techmech-keeb/OLSK60_v2/docs/images/cherry-mx-switch-views.png

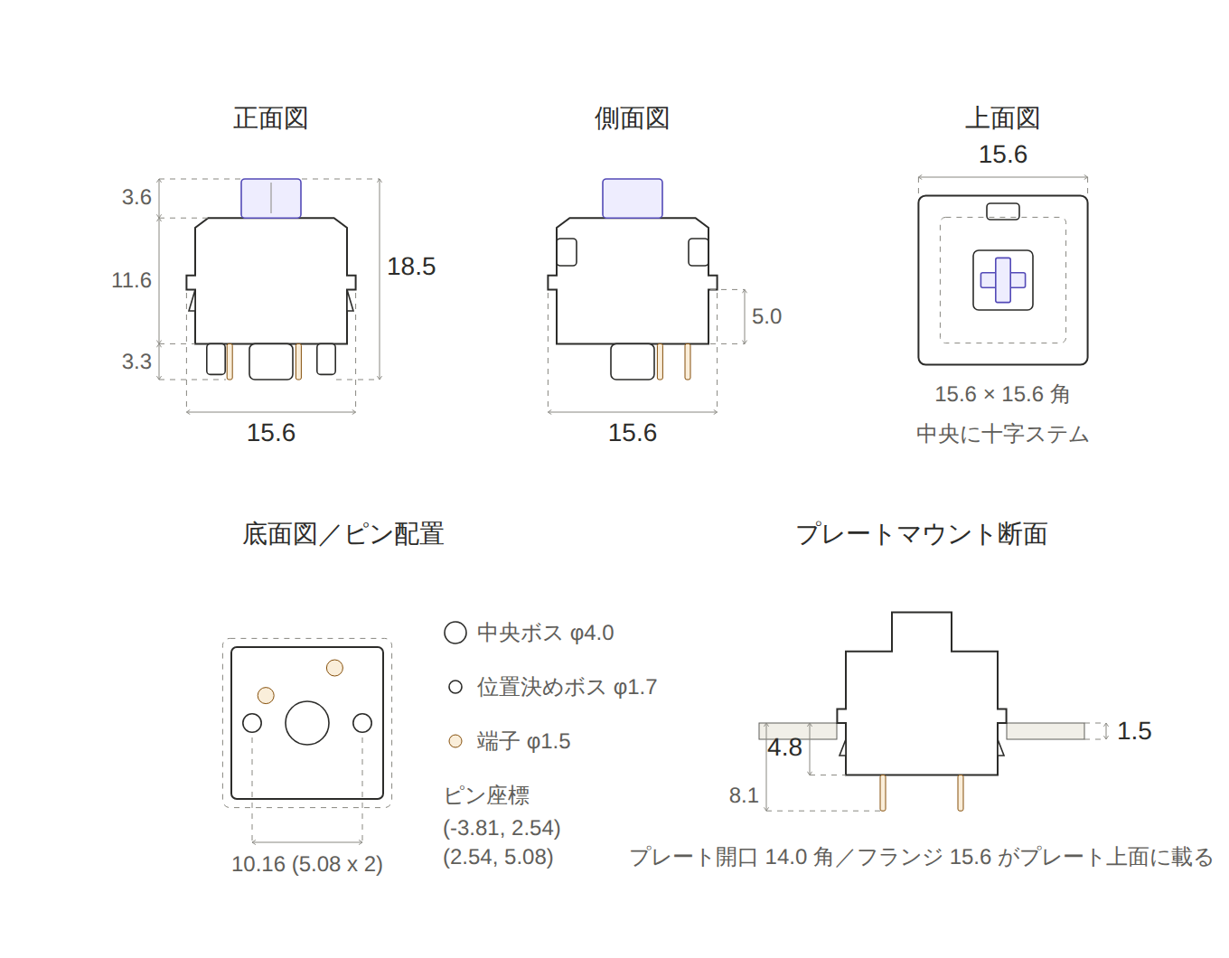
docs/images/cherry-mx-switch-views.png
