techmech-keeb/OLSK60_v2/docs/images/keycap-sizes-3split.png

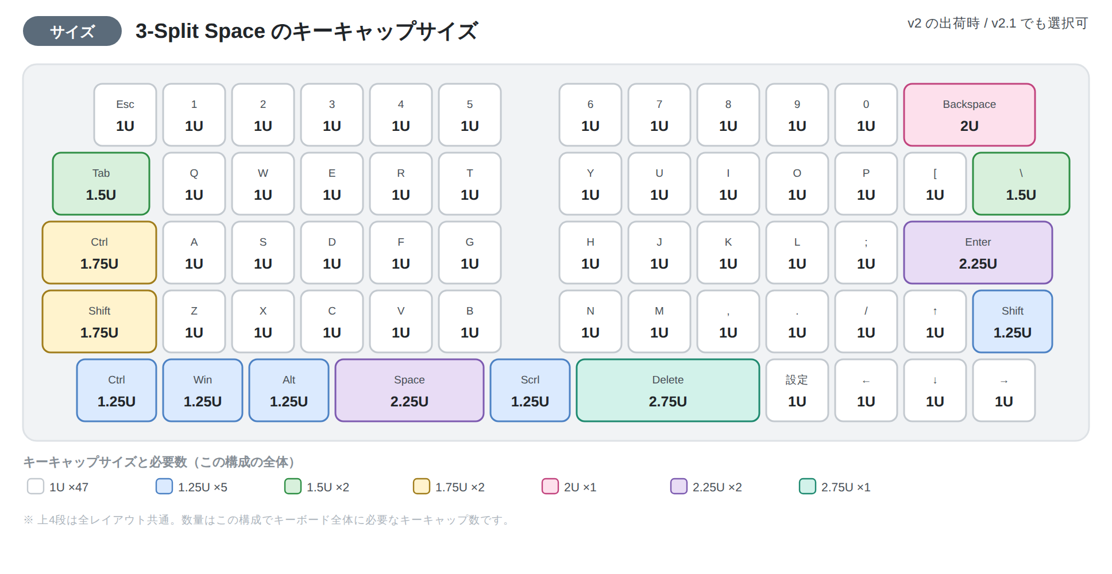
docs/images/keycap-sizes-3split.png
