techmech-keeb/OLSK60_v2/docs/images/keycap-sizes-5split.png

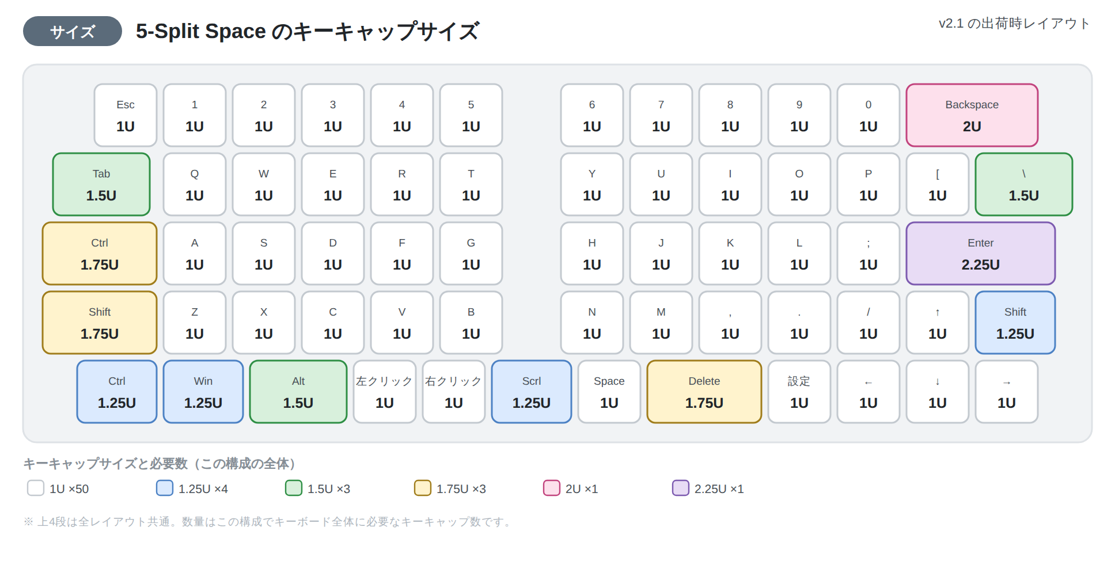
docs/images/keycap-sizes-5split.png
