techmech-keeb/OLSK60_v2/docs/images/layer2-settings.png

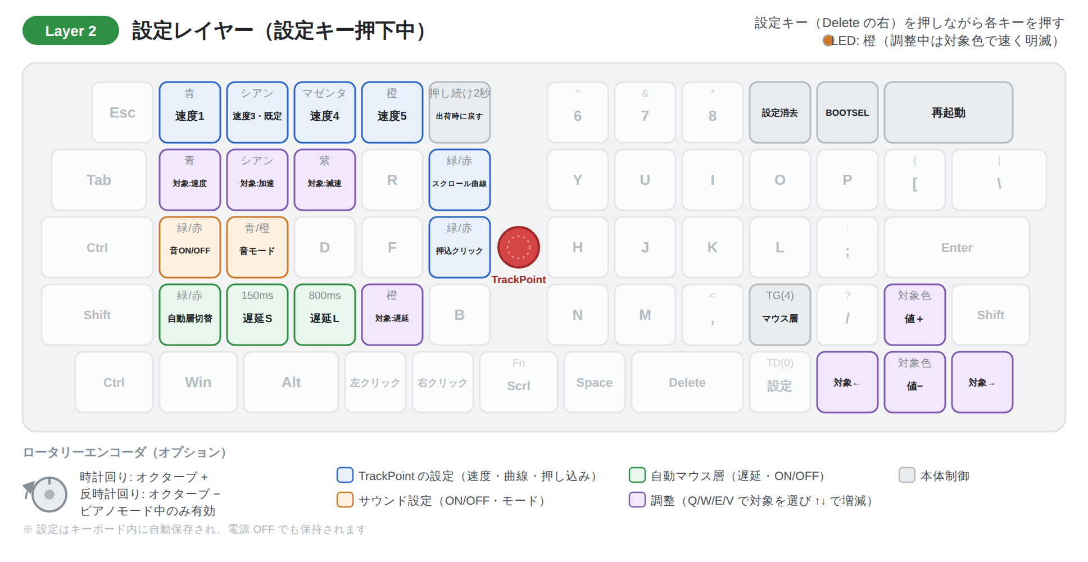
docs/images/layer2-settings.png
