techmech-keeb/OLSK60_v2/docs/images/layer3-mouse.png

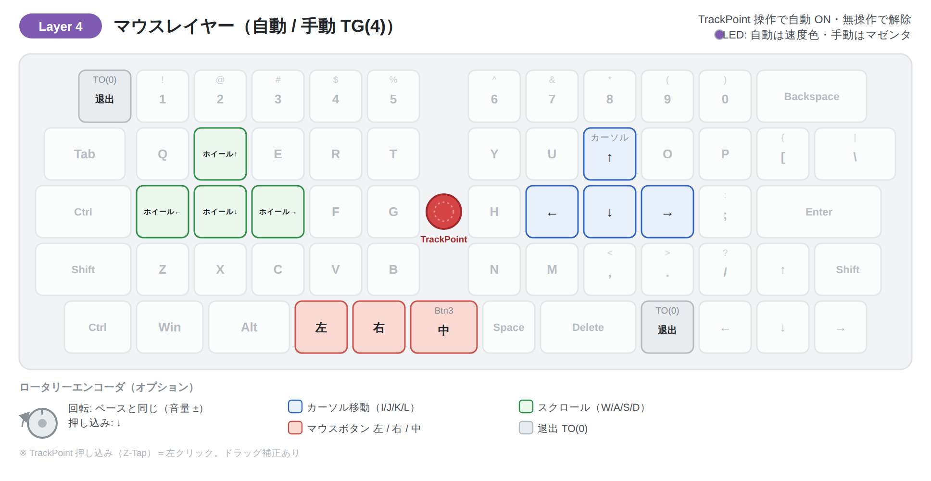
docs/images/layer3-mouse.png
