techmech-keeb/OLSK60_v2/docs/images/stab-positions.png

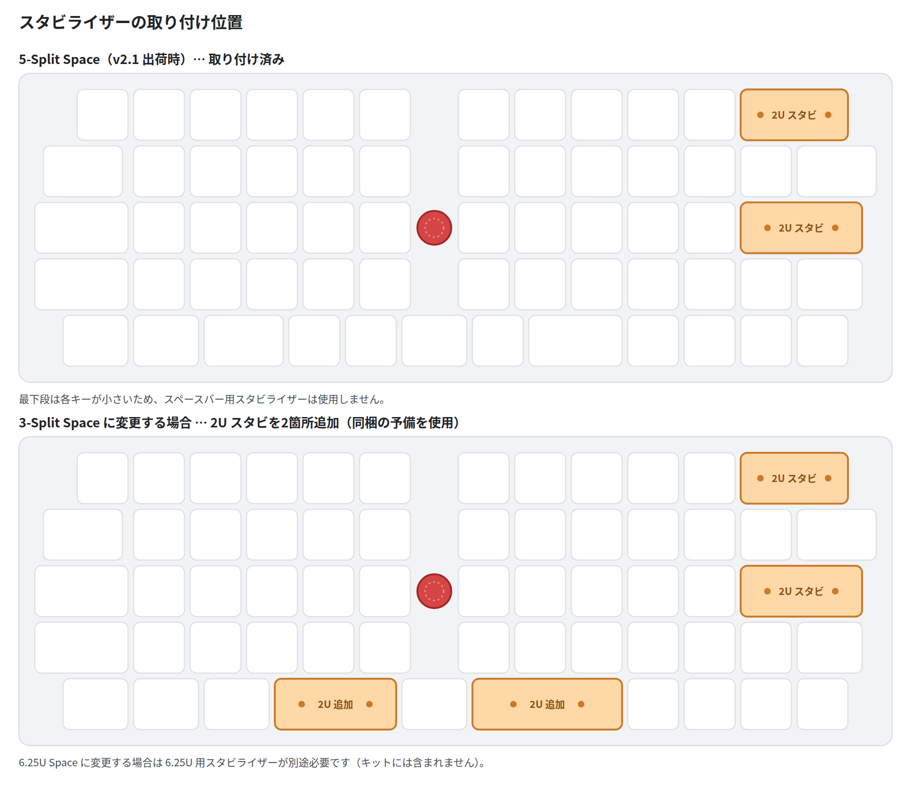
docs/images/stab-positions.png
