techmech-keeb/OLSK60_v2/docs/images/switch-mount.png

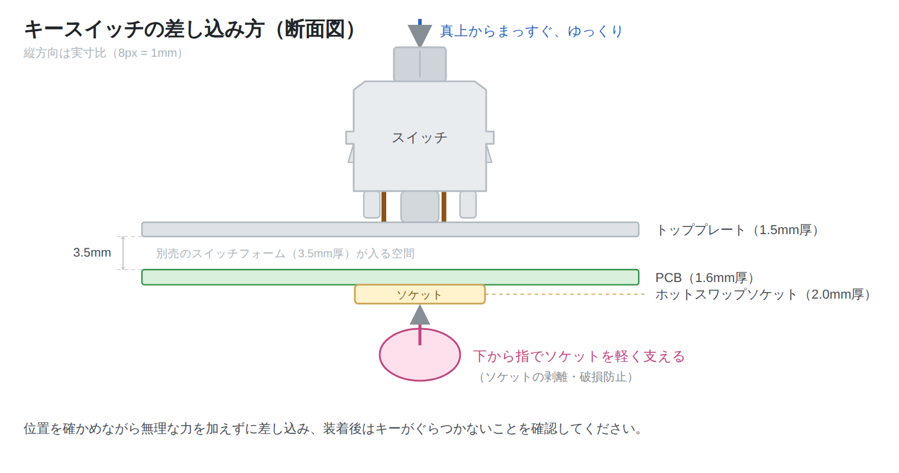
docs/images/switch-mount.png
