techmech-keeb/OLSK60_v2/docs/images/switch-pins.png

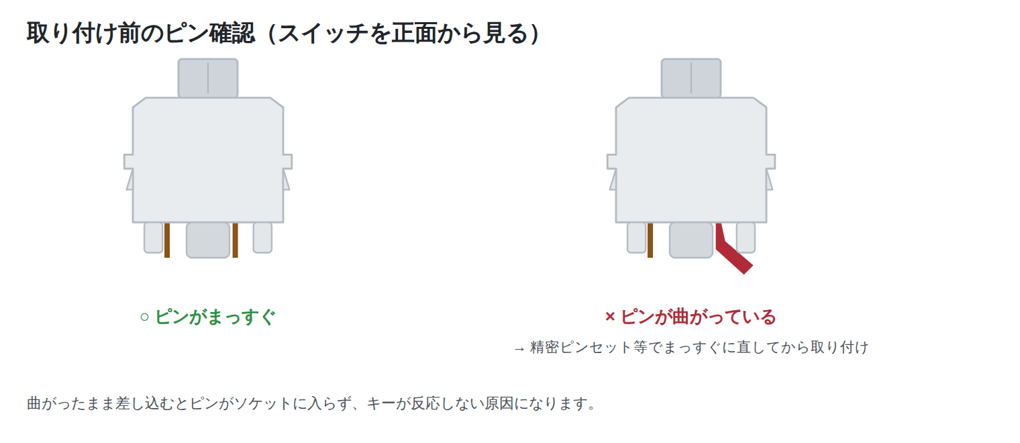
docs/images/switch-pins.png
