techmech-keeb/OLSK60_v2/docs/images/vial-unlock.png

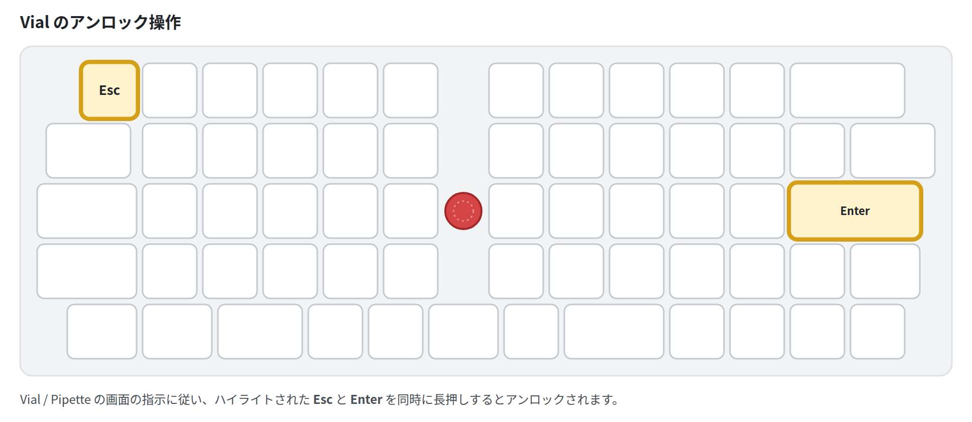
docs/images/vial-unlock.png
