techmech-keeb/OLSK60_v2/docs/images/build-exploded.png

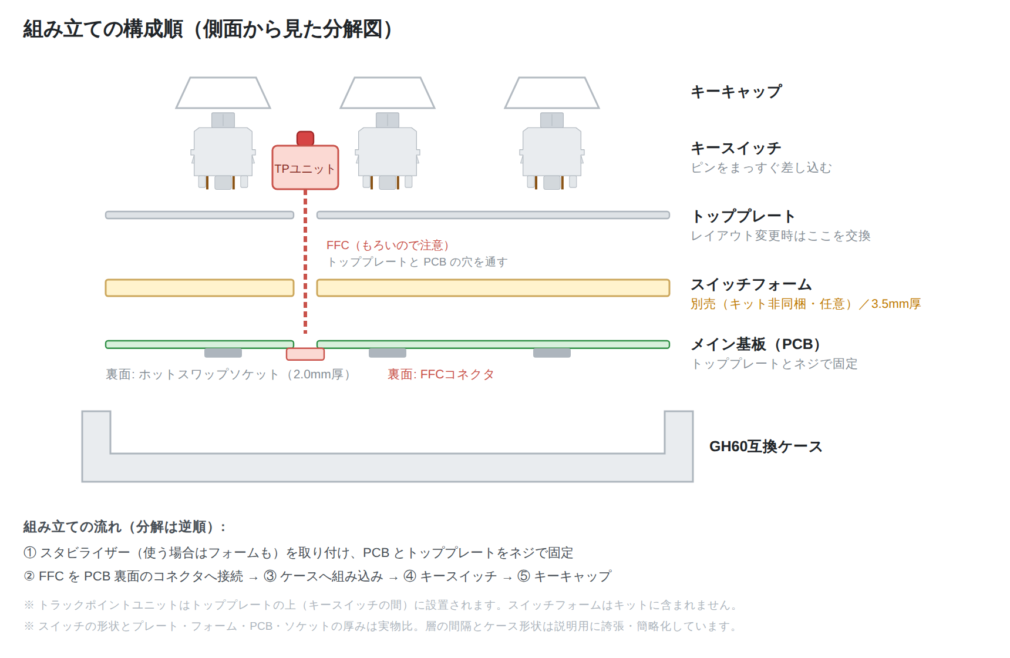
docs/images/build-exploded.png
